DoZERTY/TFE-Forest-Fire-Detection-System/Measurements/Power_consumption/plot/initial prototype/initial/initial_power_characterization_4MHz.pdf

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

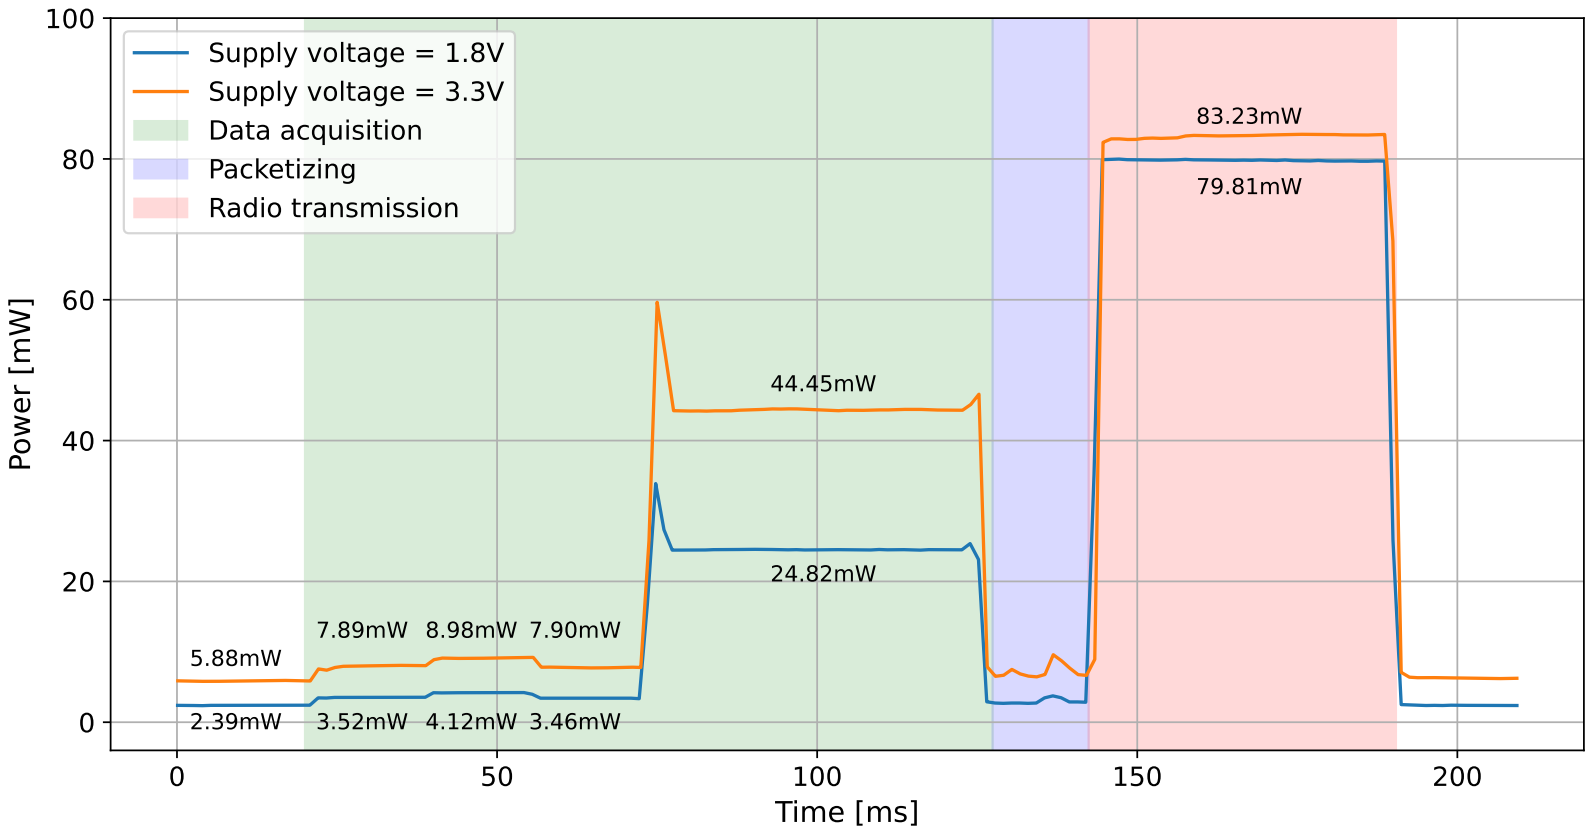
[picture p11: page 1]
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
