DoZERTY/TFE-Forest-Fire-Detection-System/Measurements/Power_consumption/plot/initial prototype/software_optimization/initial__prototype_power_50ms.pdf

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

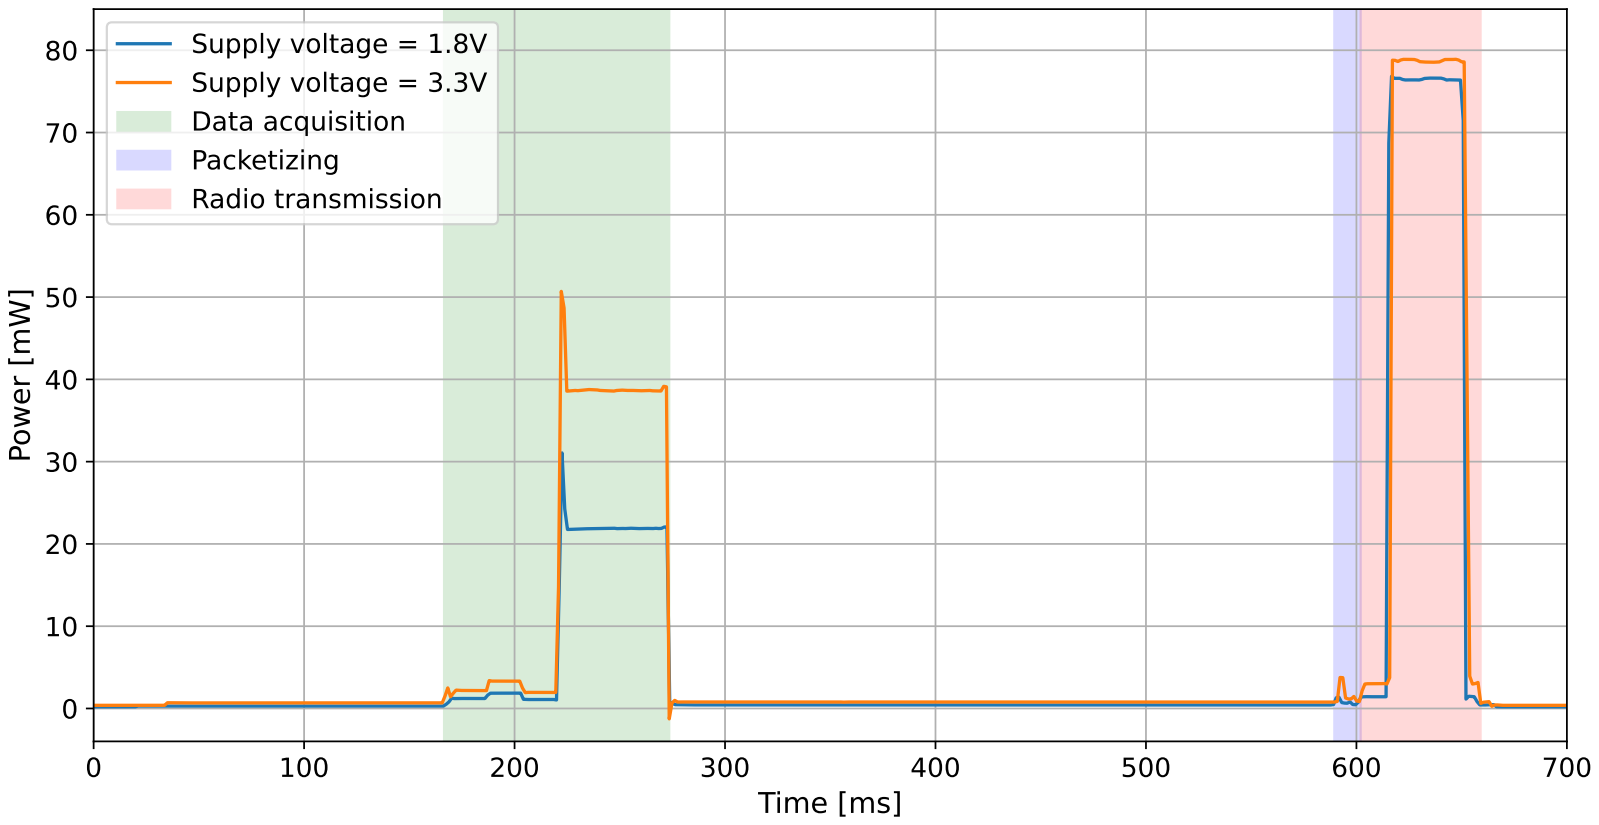
[picture p13: page 1]
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
