DoZERTY/TFE-Forest-Fire-Detection-System/Simulations/Analysis/plot/idle_initial_prototype.pdf

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

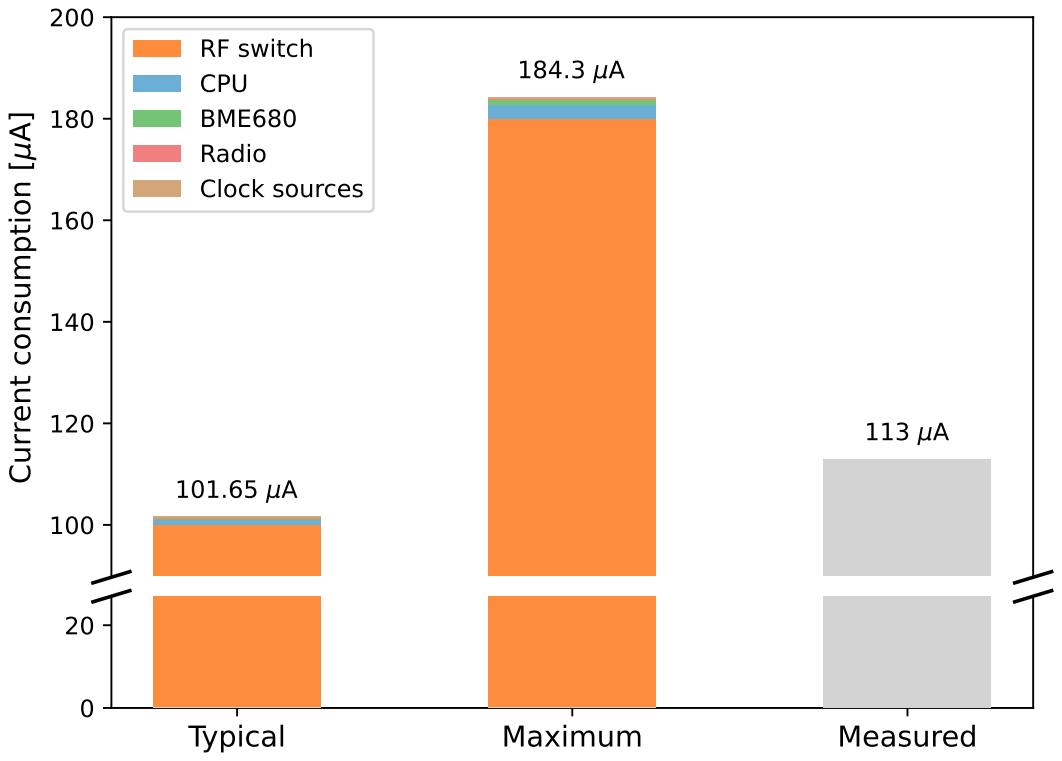
[picture p15: page 1]
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
