DoZERTY/TFE-Forest-Fire-Detection-System/Simulations/Analysis/plot/Power_consumption_vs_lambda_initial.pdf

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

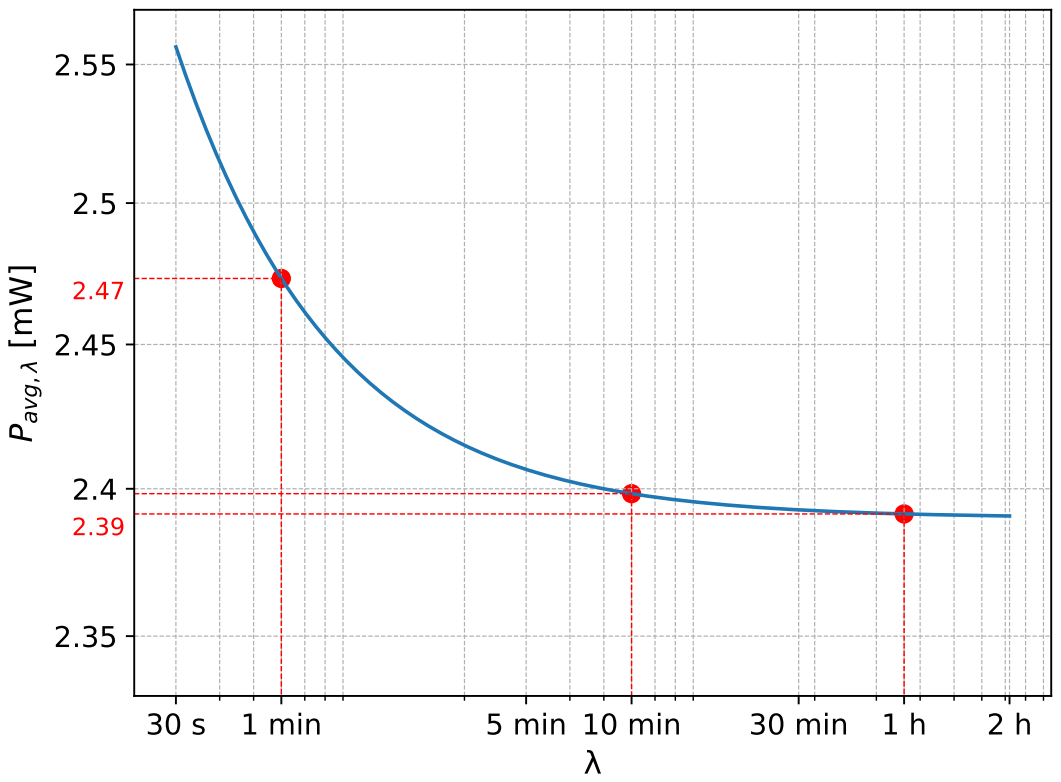
[picture p18: page 1]
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
