DoZERTY/TFE-Forest-Fire-Detection-System/Simulations/FWI/plot/error_vs_expectedFWI.pdf

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

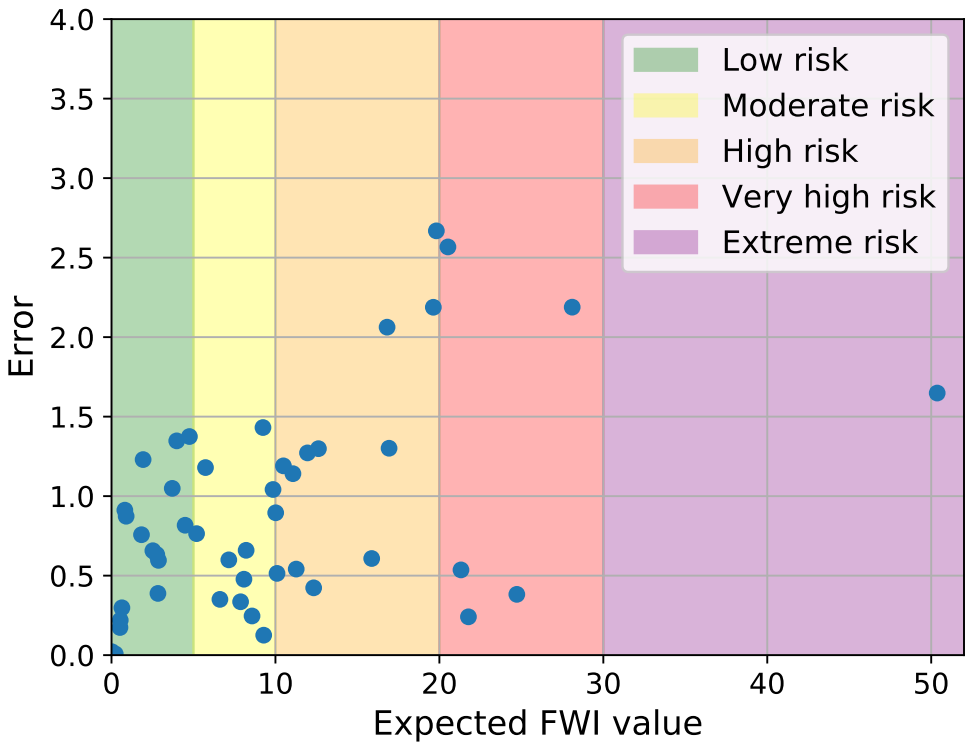
[picture p19: page 1]
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
