DoZERTY/TFE-Forest-Fire-Detection-System/Software/new_prototype/Core/Inc/main.h

#define RTC_N_PREDIV_S 10
#define RTC_PREDIV_S ((1<<RTC_N_PREDIV_S)-1)
#define RTC_PREDIV_A ((1<<(15-RTC_N_PREDIV_S))-1)
#define EN_LV_Pin GPIO_PIN_0
#define EN_LV_GPIO_Port GPIOA
#define LED_Pin GPIO_PIN_5
#define LED_GPIO_Port GPIOA
#define DRIVE_RF_Pin_Pin GPIO_PIN_7
#define DRIVE_RF_Pin_GPIO_Port GPIOA
#define DO_NOT_USE_Pin GPIO_PIN_12
#define DO_NOT_USE_GPIO_Port GPIOB
#define BTN1_Pin GPIO_PIN_11
#define BTN1_GPIO_Port GPIOA
#define BTN1_EXTI_IRQn EXTI15_10_IRQn
#define VERBOSE					0
