DoZERTY/TFE-Forest-Fire-Detection-System/Software/initial_prototype/Core/Inc/my_packet.h

/*
 * my_packet.h
 *
 *  Created on: Apr 28, 2025
 *      Author: Dorian
 *
 */

#ifndef INC_MY_PACKET_H_
#define INC_MY_PACKET_H_


#include "bme68x_defs.h"
#include "my_sensor.h"

#define SENDER_ID					1	// on one bytes : 0 to 255

#define PAYLOAD_MAX_LENGTH			64
#define USE_MAX_LENGTH				0
#define PACKET_LENGTH				8 	// in bytes, for decoding (with gas sensing)

#define PRINT_PACKET_DECODED		1	// if 1 print the numbers in addition than in hex format

#define SYNC_PACKET_NUMBER			6		// from 1 to that number
#define SYNC_PACKET_DELAY			RTC_DELAY/SYNC_PACKET_NUMBER	// in ms, between two sync packets

#if(SEND_SYNC_PACKETS)
void send_sync_packet(void);
#endif

void make_packet(struct bme68x_data *bme_data);
void send_packet(void);
void send_dummy_packet(void);
void decode_print_packet(uint8_t *payload, uint16_t size, int16_t rssi, int8_t LoraSnr_FskCfo);

#endif /* INC_MY_PACKET_H_ */
